SukkoPera/avr-fusebit-doctor/SMD-pcb/avrdoc_adapter/shuffle_avrdocusb_topscr.JPG

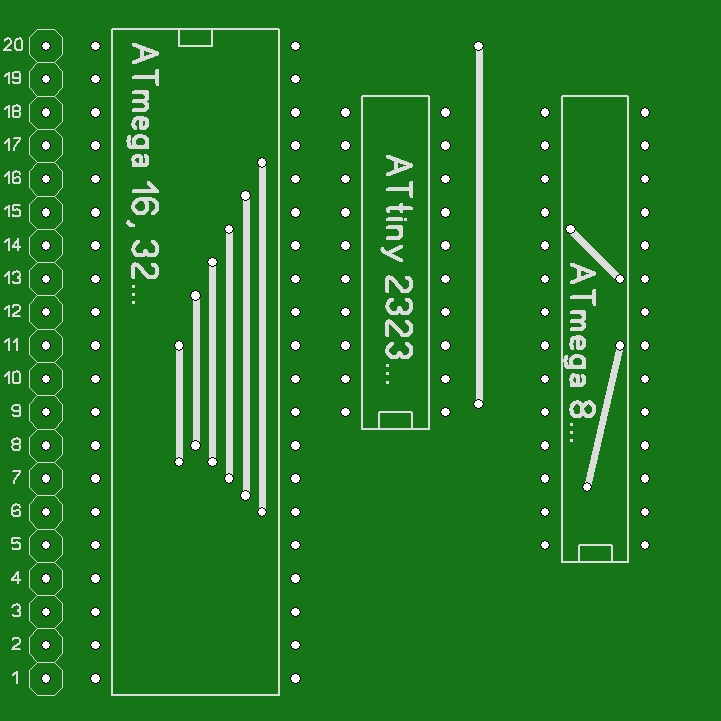
SMD-pcb/avrdoc_adapter/shuffle_avrdocusb_topscr.JPG
