SukkoPera/avr-fusebit-doctor/SMD-pcb/avrdoc_main/shuffle_avrdocusb_topscr.JPG

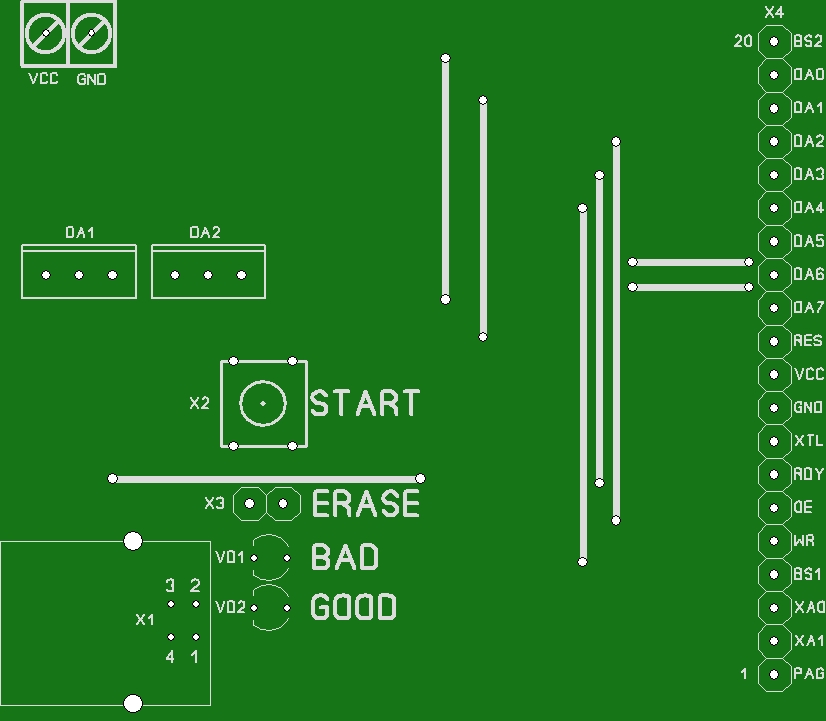
SMD-pcb/avrdoc_main/shuffle_avrdocusb_topscr.JPG
