SukkoPera/avr-fusebit-doctor/SMD-pcb/avrdoc_photos/2_avrdoc_usb_top2.JPG

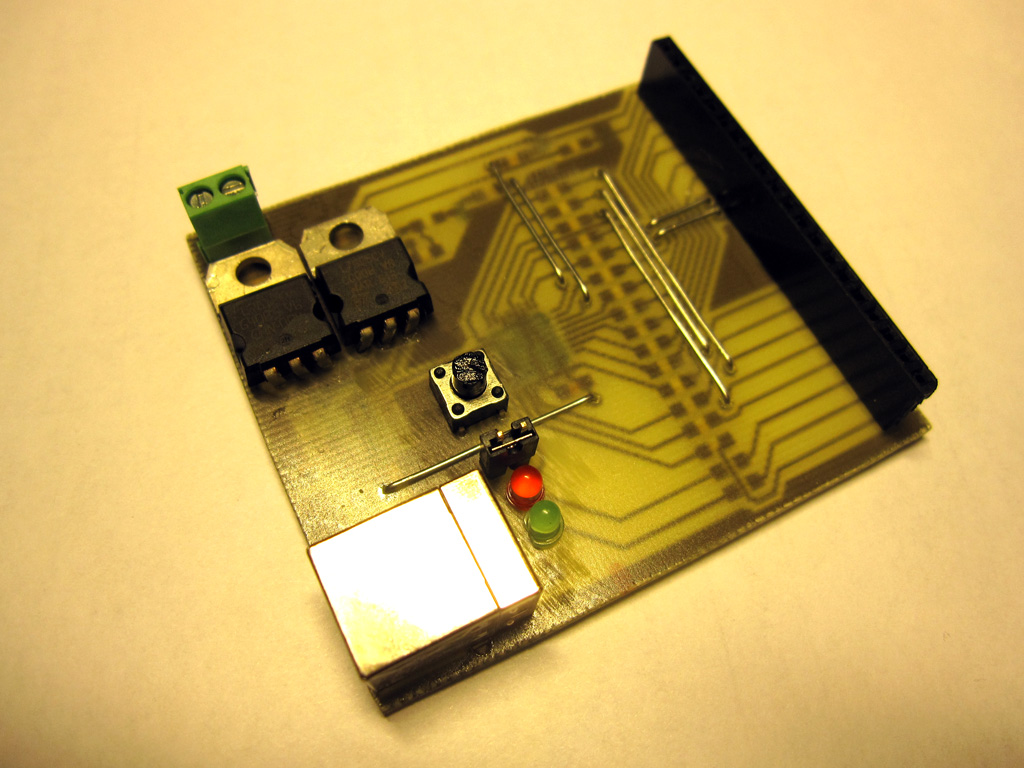
SMD-pcb/avrdoc_photos/2_avrdoc_usb_top2.JPG
