SukkoPera/avr-fusebit-doctor/SMD-pcb/avrdoc_photos/3_avrdoc_usb_bottom.JPG

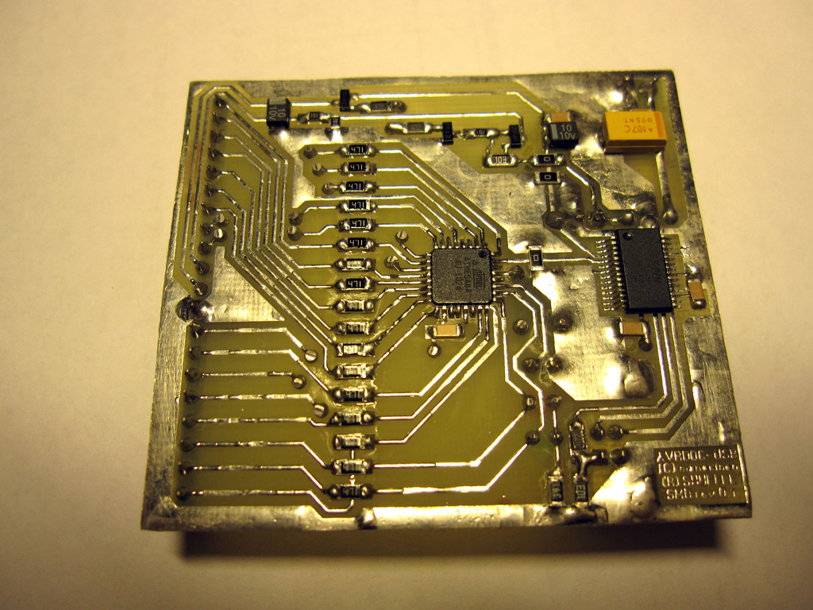
SMD-pcb/avrdoc_photos/3_avrdoc_usb_bottom.JPG
