SukkoPera/avr-fusebit-doctor/SMD-pcb/avrdoc_photos/4_avrdoc_usb_with_adapters1.jpg

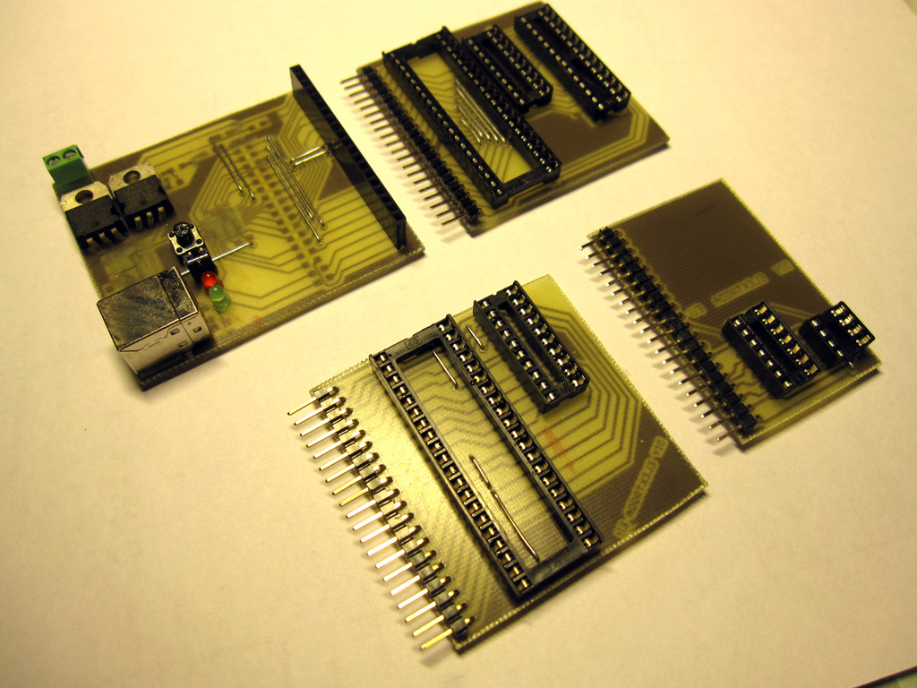
SMD-pcb/avrdoc_photos/4_avrdoc_usb_with_adapters1.jpg
