SukkoPera/avr-fusebit-doctor/SMD-pcb/avrdoc_photos/5_avrdoc_usb_with_adapters2.JPG

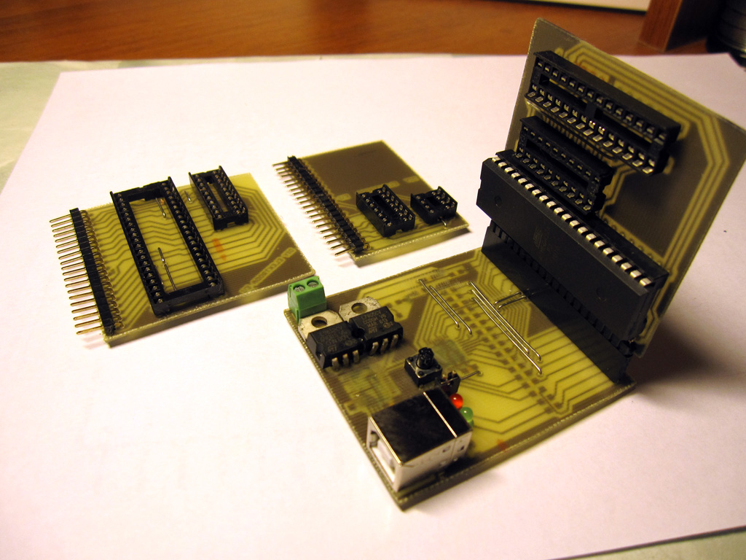
SMD-pcb/avrdoc_photos/5_avrdoc_usb_with_adapters2.JPG
