SukkoPera/avr-fusebit-doctor/sockets/8pin-hvsp-adapter.gif

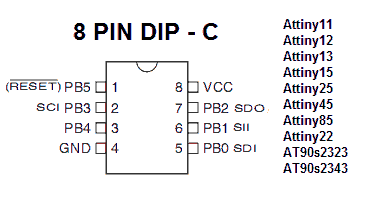
sockets/8pin-hvsp-adapter.gif
