SukkoPera/avr-fusebit-doctor/sockets/14pin-hvsp-adapter.gif

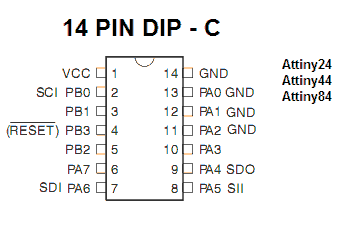
sockets/14pin-hvsp-adapter.gif
