SukkoPera/avr-fusebit-doctor/sockets/20pin-hvpp-adapter.gif

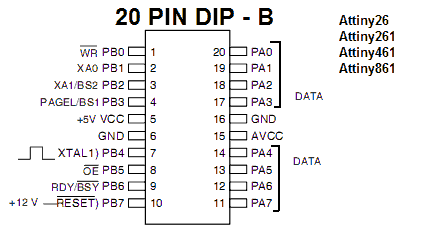
sockets/20pin-hvpp-adapter.gif
