SukkoPera/avr-fusebit-doctor/sockets/20pin-onboard.gif

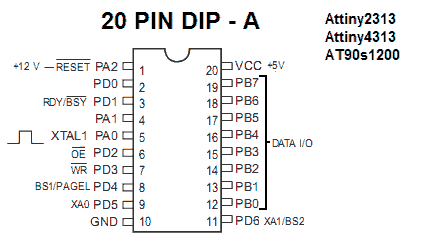
sockets/20pin-onboard.gif
