SukkoPera/avr-fusebit-doctor/sockets/40pin-hvpp-adapter.gif

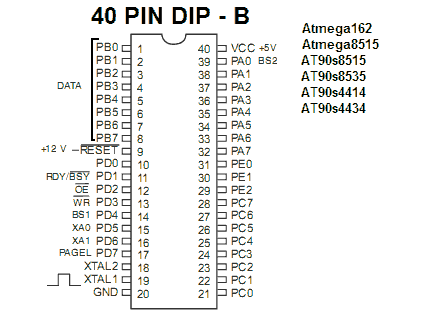
sockets/40pin-hvpp-adapter.gif
