SukkoPera/avr-fusebit-doctor/SMD-pcb/avrdoc_main/shuffle_avrdocusb_bom.jpg

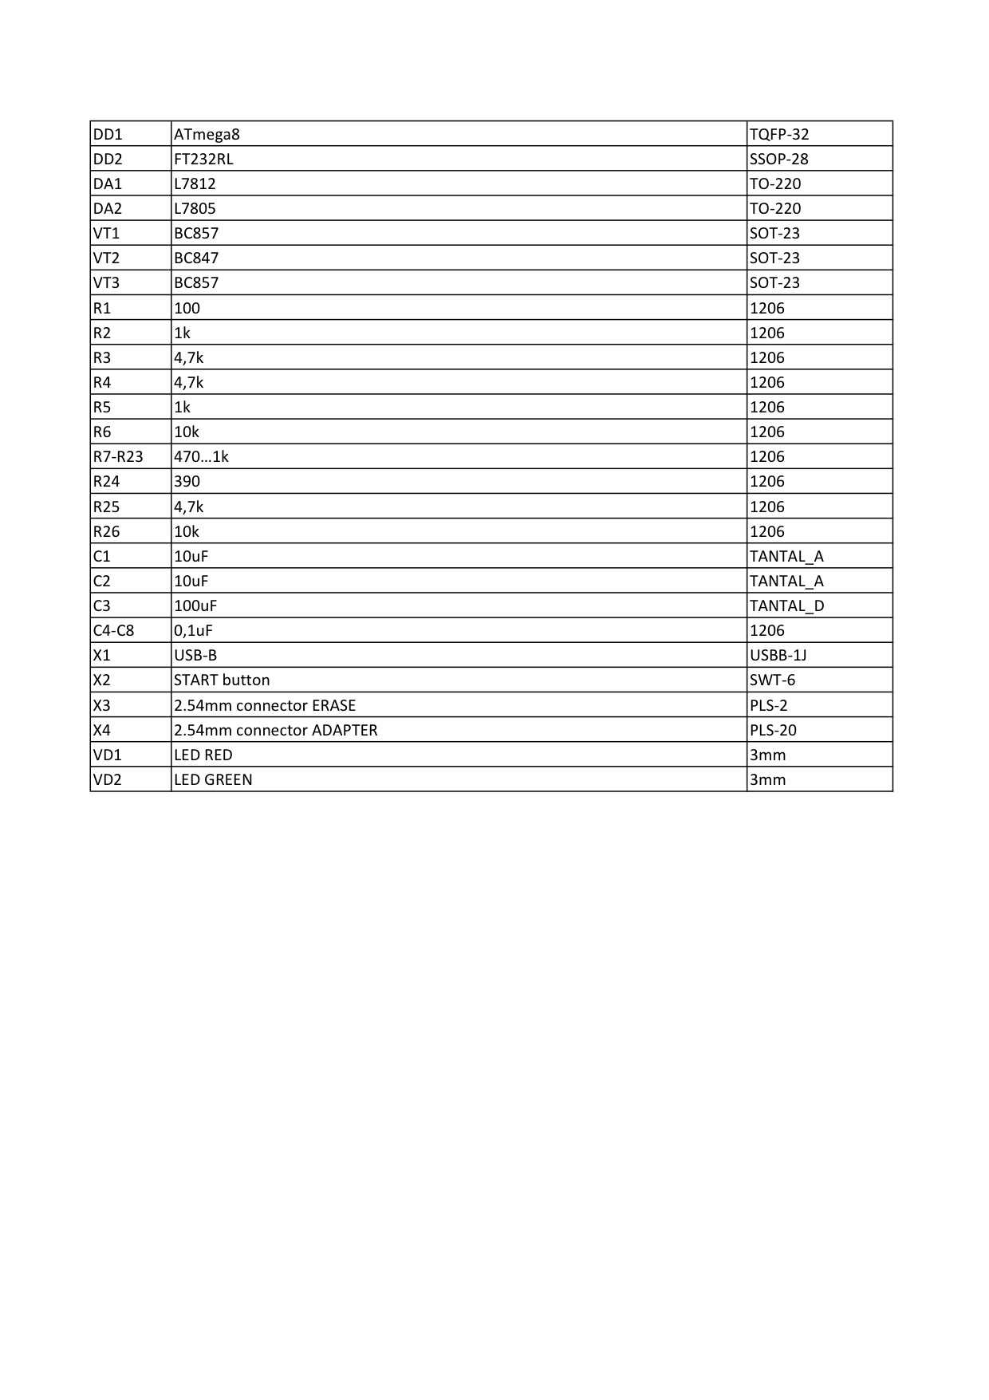
SMD-pcb/avrdoc_main/shuffle_avrdocusb_bom.jpg
