SukkoPera/avr-fusebit-doctor/sockets/wiring-help.gif

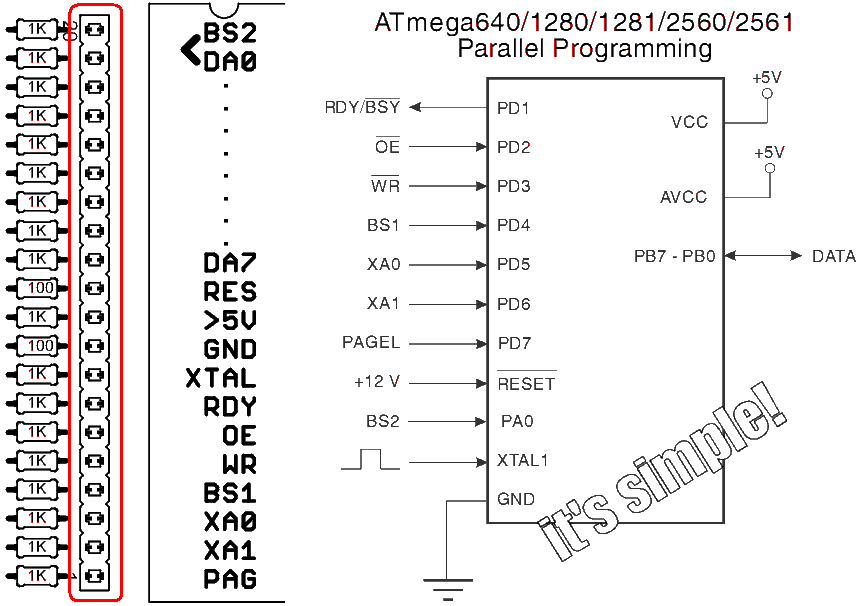
sockets/wiring-help.gif
