SukkoPera/avr-fusebit-doctor/adapters/adapter_HVSP_bottom.pdf

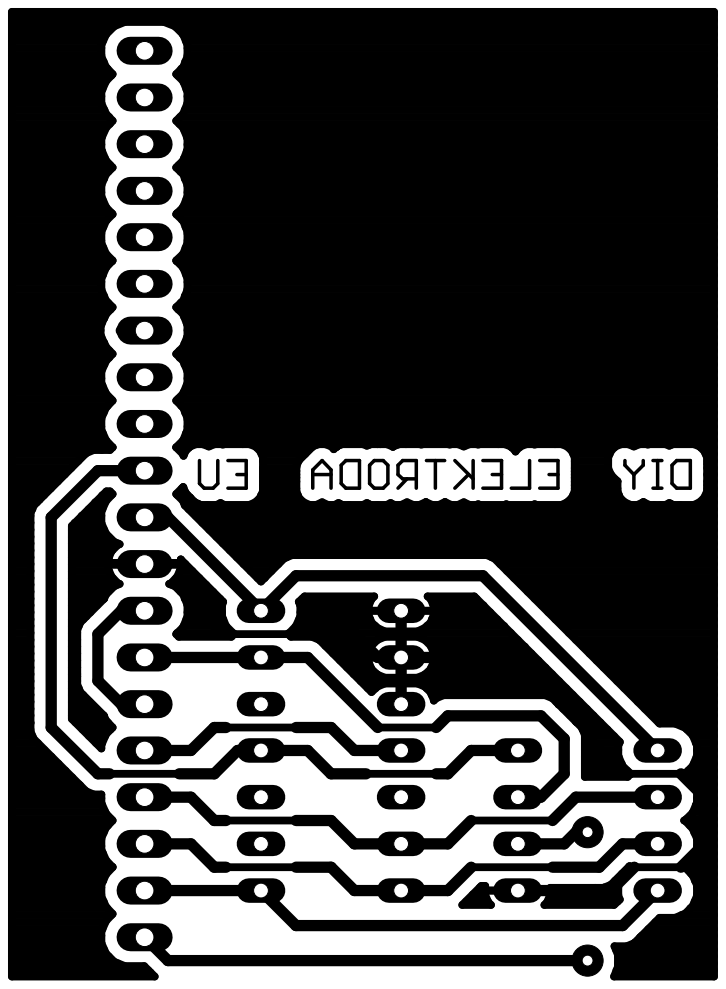
[picture p32: page 1]
