SukkoPera/avr-fusebit-doctor/adapters/adapter_HVSP_top_mirrored.pdf

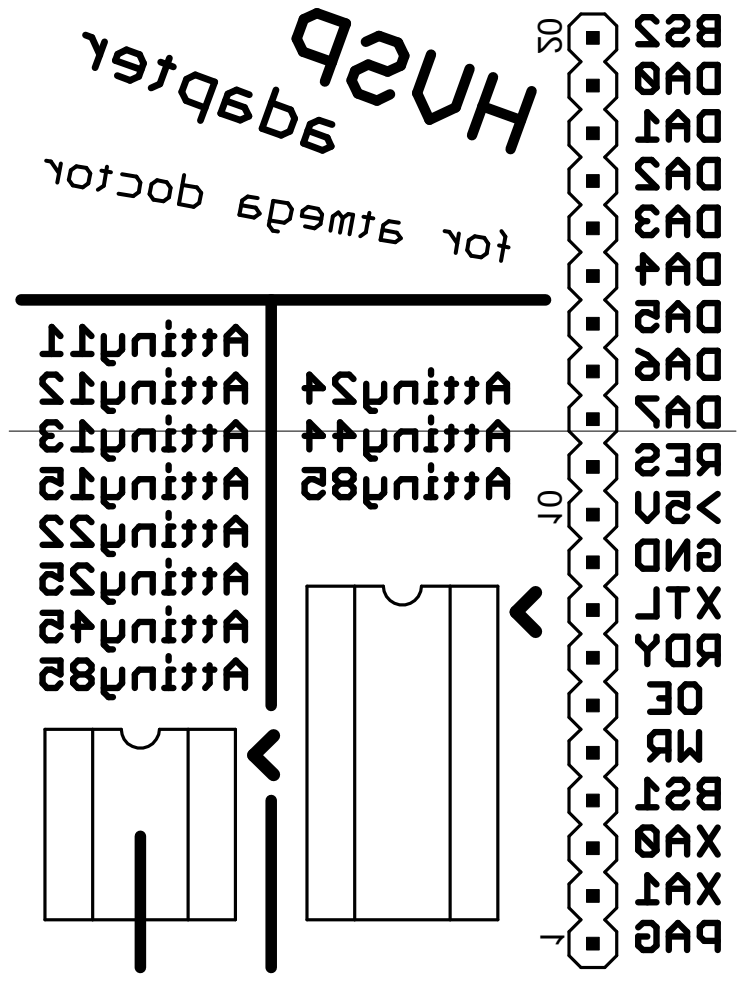
[picture p33: page 1]
