SukkoPera/avr-fusebit-doctor/SMD-pcb/avrdoc_adapter/shuffle_avrdocusb_botpcb.pdf

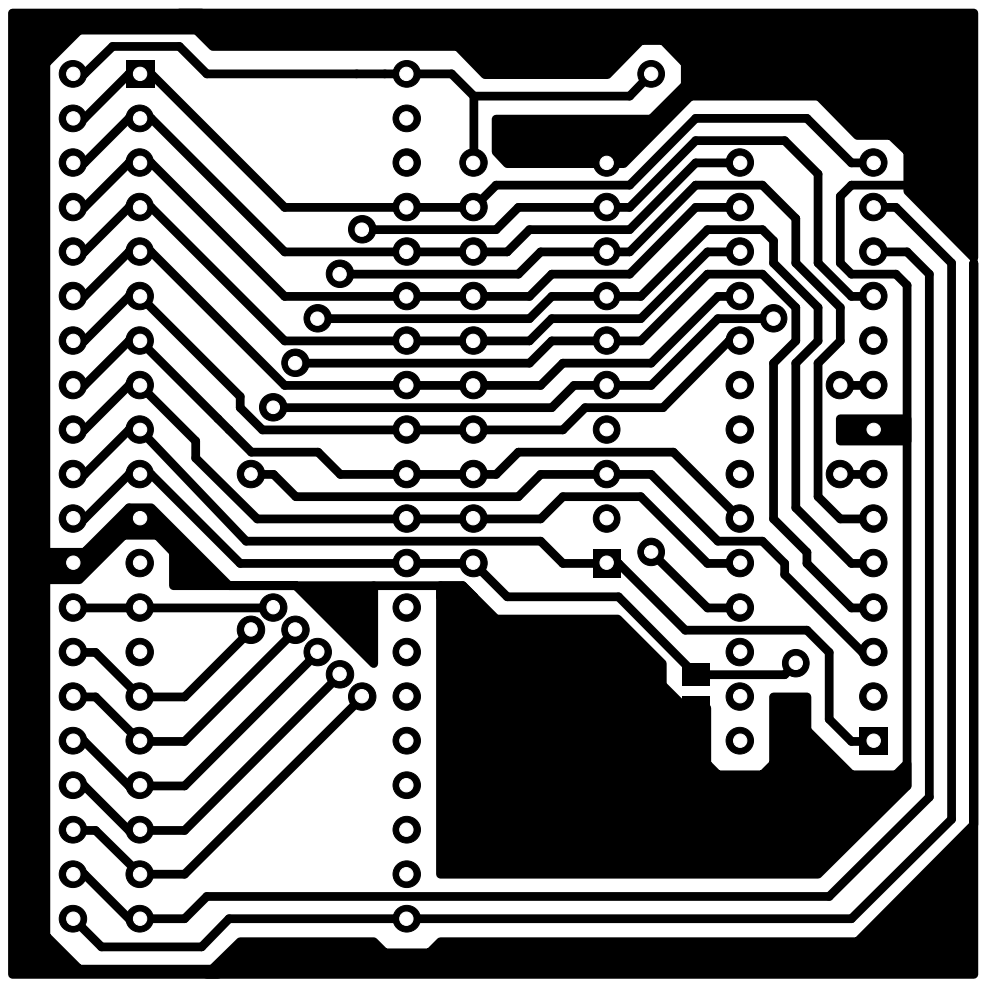
[picture p34: page 1]
