SukkoPera/avr-fusebit-doctor/SMD-pcb/avrdoc_adapter/shuffle_avrdocusb_toppcb.pdf

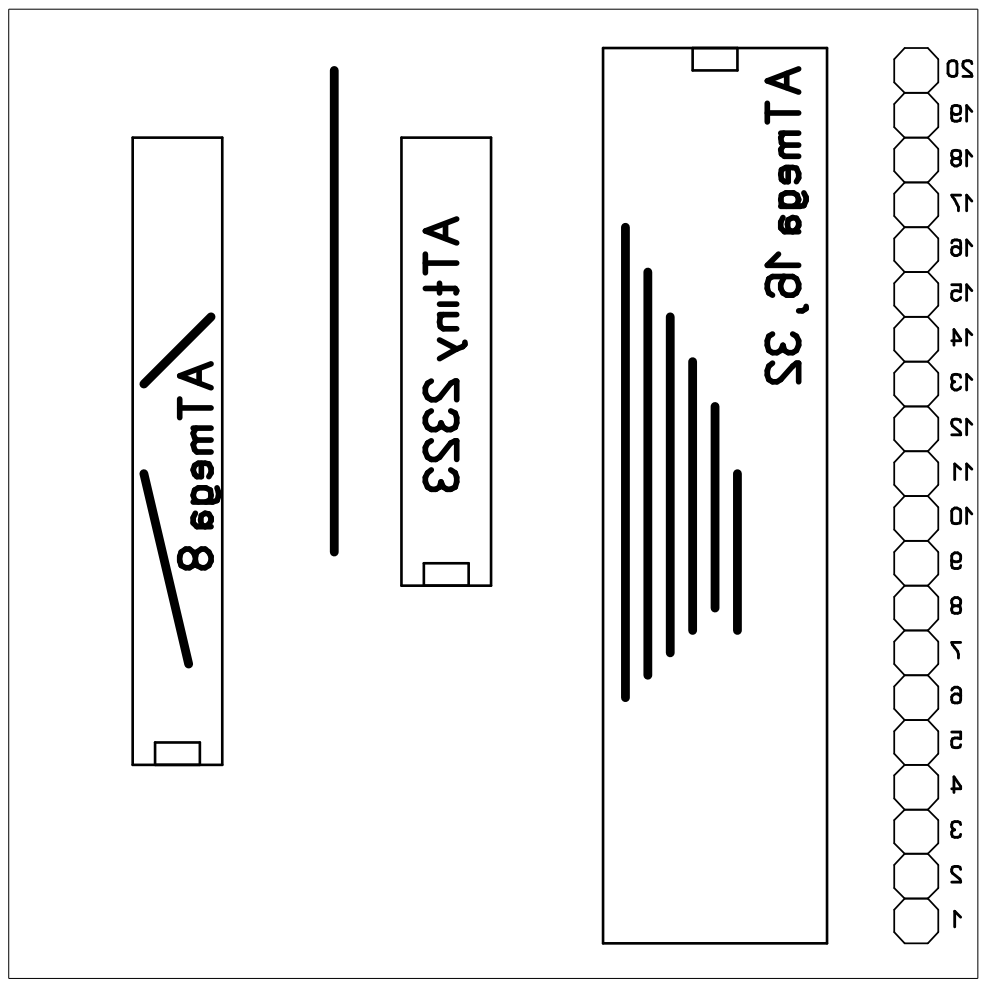
[picture p35: page 1]
