SukkoPera/avr-fusebit-doctor/SMD-pcb/avrdoc_main/shuffle_avrdocusb_botpcb.pdf

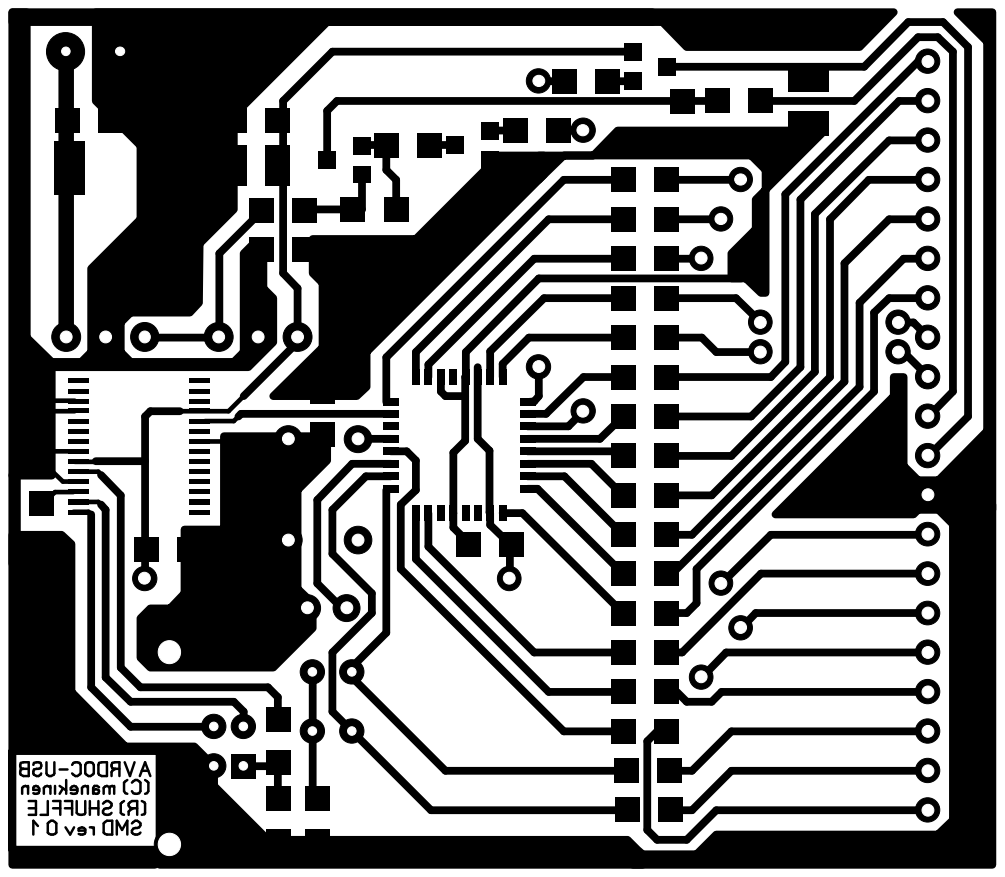
[picture p36: page 1]
