SukkoPera/avr-fusebit-doctor/SMD-pcb/avrdoc_main/shuffle_avrdocusb_toppcb.pdf

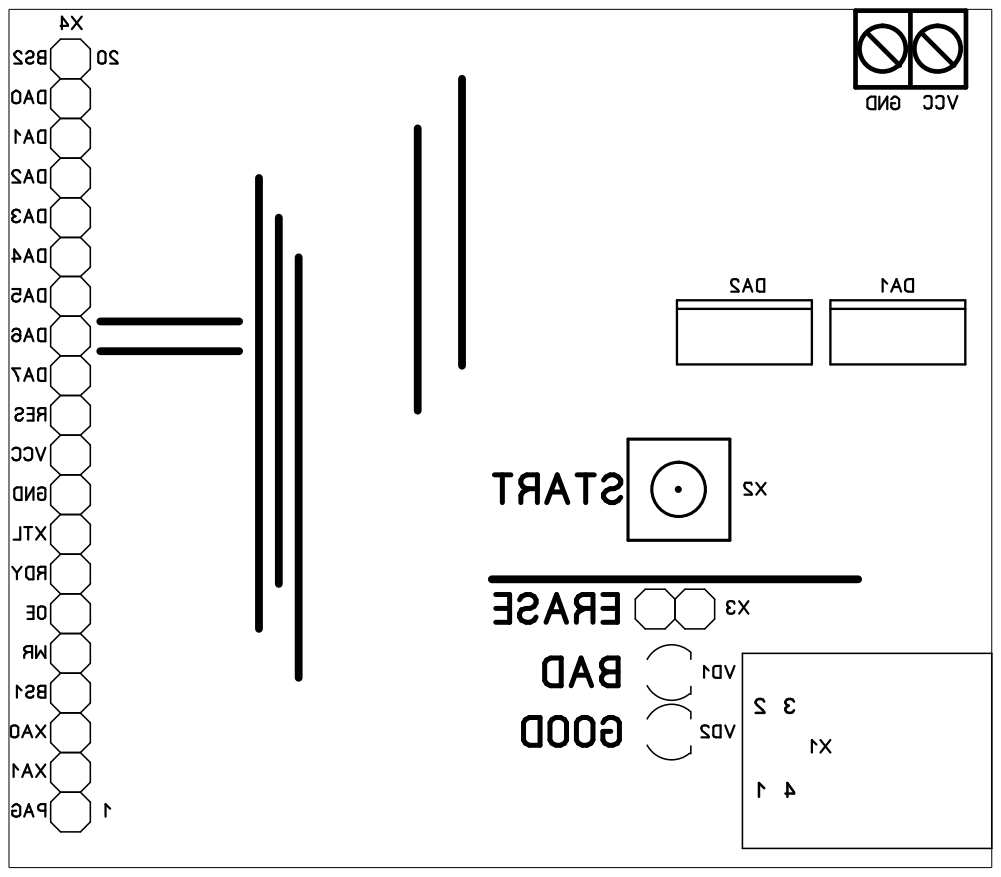
[picture p37: page 1]
